JMU-Wearable-Computing/haptic-glove/Images/Tutorial Photos/PlatformIO Setup/bus_io_library.png

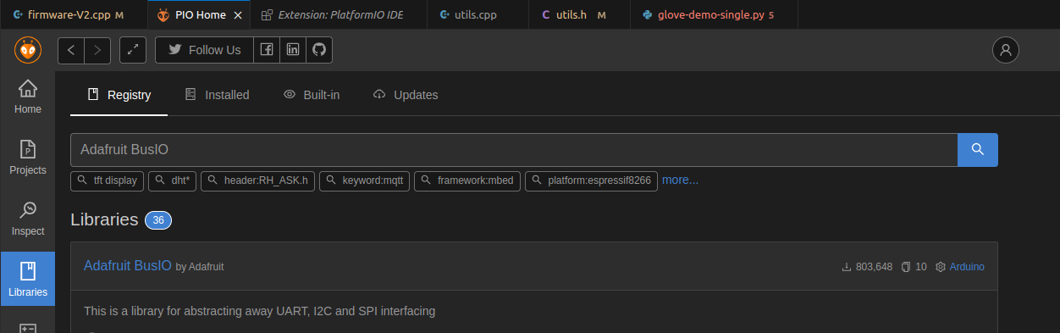
Images/Tutorial Photos/PlatformIO Setup/bus_io_library.png
