JMU-Wearable-Computing/haptic-glove/Images/Tutorial Photos/PlatformIO Setup/file_structure.png

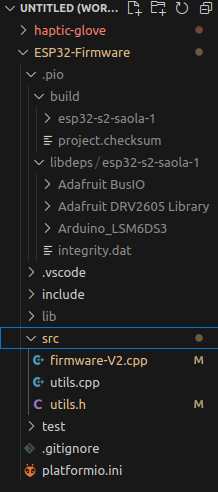
Images/Tutorial Photos/PlatformIO Setup/file_structure.png
