JMU-Wearable-Computing/haptic-glove/Images/Tutorial Photos/PlatformIO Setup/open_serial.png

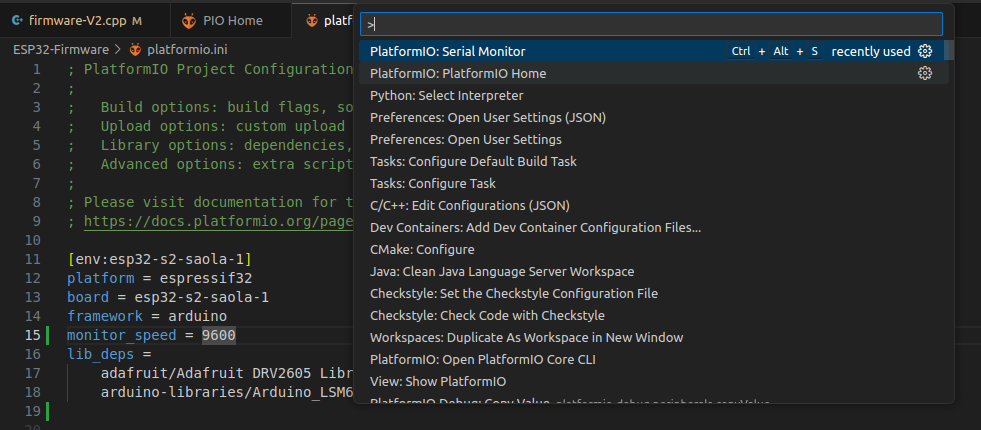
Images/Tutorial Photos/PlatformIO Setup/open_serial.png
