JMU-Wearable-Computing/haptic-glove/Images/Tutorial Photos/PlatformIO Setup/serial_output.png

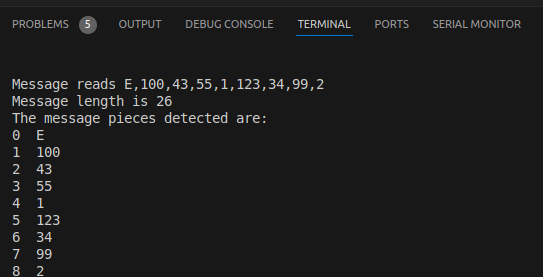
Images/Tutorial Photos/PlatformIO Setup/serial_output.png
