JMU-Wearable-Computing/haptic-glove/Images/Tutorial Photos/PlatformIO Setup/set_baud_rate.png

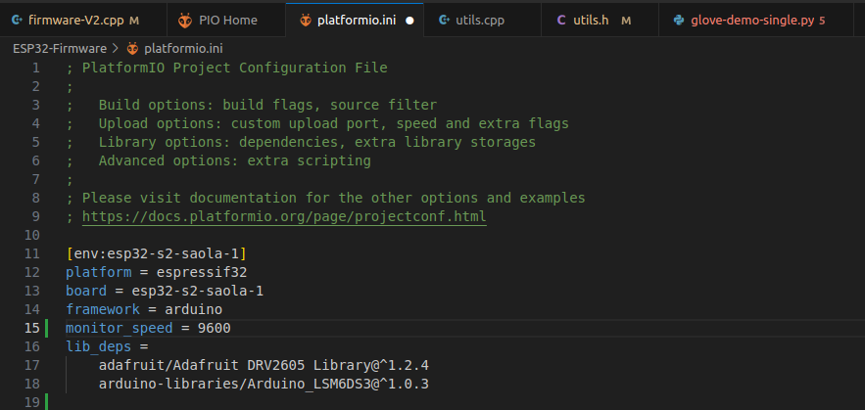
Images/Tutorial Photos/PlatformIO Setup/set_baud_rate.png
