JMU-Wearable-Computing/haptic-glove/Python/joint_angle_test_data_002.csv

Format Version | 1.23 | Take Name | joint_angle_test_data_002 | Take Notes |  | Capture Frame Rate | 120.000000 | Export Frame Rate | 120.000000 | Capture Start Time | 2024-09-20 12.51.27.389 PM | Capture Start Frame | 91932359 | Total Frames in Take | 2987 | Total Exported Frames | 2987 | Rotation Type | Quaternion | Length Units | Millimeters | Coordinate Space | Local
 | Type | Marker | Marker | Marker | Marker | Marker | Marker | Marker | Marker | Marker
 | Name | Elbow | Elbow | Elbow | Hand | Hand | Hand | Shoulder | Shoulder | Shoulder
 | ID | 27E4CEA3EA24707811EF | 27E4CEA3EA24707811EF | 27E4CEA3EA24707811EF | 2808CEA3EA24707811EF | 2808CEA3EA24707811EF | 2808CEA3EA24707811EF | 2805CEA3EA24707811EF | 2805CEA3EA24707811EF | 2805CEA3EA24707811EF
 |  | Position | Position | Position | Position | Position | Position | Position | Position | Position
Frame | Time (Seconds) | X | Y | Z | X | Y | Z | X | Y | Z
0 | 0.000000 | -106.629082 | 28.969299 | 745.029114 | 394.950256 | 6.998325 | 980.493958 | 123.977539 | 14.865740 | 248.449341
1 | 0.008000 | -106.635483 | 28.973684 | 745.034973 | 394.960968 | 6.996509 | 980.489136 | 123.973701 | 14.865225 | 248.452805
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
