JMU-Wearable-Computing/haptic-glove/Python/joint_angle_test_data_005.csv

Format Version | 1.23 | Take Name | joint_angle_test_data_005 | Take Notes |  | Capture Frame Rate | 120.000000 | Export Frame Rate | 120.000000 | Capture Start Time | 2024-09-20 01.28.16.486 PM | Capture Start Frame | 92197447 | Total Frames in Take | 1209 | Total Exported Frames | 1209 | Rotation Type | Quaternion | Length Units | Millimeters | Coordinate Space | Local
 | Type | Marker | Marker | Marker | Marker | Marker | Marker | Marker | Marker | Marker
 | Name | Elbow | Elbow | Elbow | Hand | Hand | Hand | Shoulder | Shoulder | Shoulder
 | ID | 289DCEA3EA24707811EF | 289DCEA3EA24707811EF | 289DCEA3EA24707811EF | 289CCEA3EA24707811EF | 289CCEA3EA24707811EF | 289CCEA3EA24707811EF | 289ACEA3EA24707811EF | 289ACEA3EA24707811EF | 289ACEA3EA24707811EF
 |  | Position | Position | Position | Position | Position | Position | Position | Position | Position
Frame | Time (Seconds) | X | Y | Z | X | Y | Z | X | Y | Z
0 | 0.000000 | -500.934601 | 1016.669861 | 1447.266968 | -338.306641 | 849.596924 | 1579.394409 | -453.653961 | 1358.664795 | 1405.358643
1 | 0.008000 | -499.620697 | 1016.606445 | 1447.831787 | -332.645905 | 852.768494 | 1579.212402 | -453.719696 | 1358.724243 | 1405.263306
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
