JMU-Wearable-Computing/haptic-glove/Python/joint_angle_test_data_006.csv

Format Version | 1.23 | Take Name | joint_angle_test_data_006 | Take Notes |  | Capture Frame Rate | 120.000000 | Export Frame Rate | 120.000000 | Capture Start Time | 2024-09-25 02.39.40.245 PM | Capture Start Frame | 144550676 | Total Frames in Take | 3130 | Total Exported Frames | 3130 | Rotation Type | Quaternion | Length Units | Millimeters | Coordinate Space | Local
 | Type | Marker | Marker | Marker | Marker | Marker | Marker | Marker | Marker | Marker
 | Name | Elbow | Elbow | Elbow | Hand | Hand | Hand | Shoulder | Shoulder | Shoulder
 | ID | 295BCEA3EA24707811EF | 295BCEA3EA24707811EF | 295BCEA3EA24707811EF | 2959CEA3EA24707811EF | 2959CEA3EA24707811EF | 2959CEA3EA24707811EF | 2953CEA3EA24707811EF | 2953CEA3EA24707811EF | 2953CEA3EA24707811EF
 |  | Position | Position | Position | Position | Position | Position | Position | Position | Position
Frame | Time (Seconds) | X | Y | Z | X | Y | Z | X | Y | Z
0 | 0.000000 | -357.986481 | 23.156046 | 519.461670 | 173.546631 | 30.231720 | 318.815765 | 195.666138 | 14.611786 | 385.810516
1 | 0.008000 | -357.984253 | 23.146061 | 519.462341 | 173.605820 | 30.106300 | 318.782104 | 195.663895 | 14.608956 | 385.808167
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
