JMU-Wearable-Computing/haptic-glove/Python/joint_angle_test_data_1_001.csv

1.23 | Capture Frame Rate | 120 | Export Frame Rate
Type | Rigid Body | Rigid Body | Rigid Body | Rigid Body | Rigid Body | Rigid Body | Rigid Body | Rigid Body | Rigid Body
Name | Shoulder_Suit | Shoulder_Suit | Shoulder_Suit | Elbow_Suit | Elbow_Suit | Elbow_Suit | Hand_Suit | Hand_Suit | Hand_Suit
ID | 5F10C191754A11EF7E5C15E596CCCB90 | 5F10C191754A11EF7E5C15E596CCCB90 | 5F10C191754A11EF7E5C15E596CCCB90 | 66B905C7754A11EF7E5C15E596CCCB90 | 66B905C7754A11EF7E5C15E596CCCB90 | 66B905C7754A11EF7E5C15E596CCCB90 | 70C6742A754A11EF7E5C15E596CCCB90 | 70C6742A754A11EF7E5C15E596CCCB90 | 70C6742A754A11EF7E5C15E596CCCB90
 | Position | Position | Position | Position | Position | Position | Position | Position | Position
Time (Seconds) | X | Y | Z | X | Y | Z | X | Y | Z
0 | -184.000488 | 1430.728027 | 28.554445 | -229.980042 | 1120.384644 | -6.191123 | -218.839157 | 900.816956 | 105.278915
0.008 | -184.019669 | 1430.710693 | 28.531429 | -230.00647 | 1120.368164 | -6.17447 | -218.86055 | 900.810669 | 105.257973
0.017 | -184.02475 | 1430.683472 | 28.518126 | -230.017319 | 1120.360596 | -6.173347 | -218.916107 | 900.781982 | 105.265892
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
