JMU-Wearable-Computing/haptic-glove/Arduino/Feedback-Pattern-Demos/DRV-demo-basic/DRV-demo-basic.ino

#include <Wire.h>
#include "Adafruit_DRV2605.h"

Adafruit_DRV2605 drv1;
Adafruit_DRV2605 drv2;
#define TCAADDR 0x70

// Select which driver to talk to
void tcaselect(uint8_t i) {
  if (i > 7) return;
 
  Wire.beginTransmission(TCAADDR);
  Wire.write(1 << i);
  Wire.endTransmission();  
}

void setup() {
  Serial.begin(9600);
  Wire.begin();
  Serial.println("Adafruit DRV2605 Basic test");

  // Set up first driver
  tcaselect(0);
  if (! drv1.begin()) {
    Serial.println("Could not find DRV2605");
    while (1) delay(10);
  }
 
  drv1.selectLibrary(1);
  
  // I2C trigger by sending 'go' command 
  // default, internal trigger when sending GO command
  drv1.setMode(DRV2605_MODE_INTTRIG);

  // Set up second driver
  tcaselect(1);
  if (! drv2.begin()) {
    Serial.println("Could not find second DRV2605");
    while (1) delay(10);
  }
 
  drv2.selectLibrary(1);
  
  // I2C trigger by sending 'go' command 
  // default, internal trigger when sending GO command
  drv2.setMode(DRV2605_MODE_INTTRIG);
}

uint8_t effect = 1;

void loop() {
//  Serial.print("Effect #"); Serial.println(effect);

   if (effect == 1) {
    Serial.println("11.2 Waveform Library Effects List");
  }

  if (effect == 1) {
    Serial.println(F("1 − Strong Click - 100%"));
  }
  if (effect == 2) {
    Serial.println(F("2 − Strong Click - 60%"));
  }
  if (effect == 3) {
    Serial.println(F("3 − Strong Click - 30%"));
  }
  if (effect == 4) {
    Serial.println(F("4 − Sharp Click - 100%"));
  }
  if (effect == 5) {
    Serial.println(F("5 − Sharp Click - 60%"));
  }
  if (effect == 6) {
    Serial.println(F("6 − Sharp Click - 30%"));
  }
  if (effect == 7) {
    Serial.println(F("7 − Soft Bump - 100%"));
  }
  if (effect == 8) {
    Serial.println(F("8 − Soft Bump - 60%"));
  }
  if (effect == 9) {
    Serial.println(F("9 − Soft Bump - 30%"));
  }
  if (effect == 10) {
    Serial.println(F("10 − Double Click - 100%"));
  }
  if (effect == 11) {
    Serial.println(F("11 − Double Click - 60%"));
  }
  if (effect == 12) {
    Serial.println(F("12 − Triple Click - 100%"));
  }
  if (effect == 13) {
    Serial.println(F("13 − Soft Fuzz - 60%"));
  }
  if (effect == 14) {
    Serial.println(F("14 − Strong Buzz - 100%"));
  }
  if (effect == 15) {
    Serial.println(F("15 − 750 ms Alert 100%"));
  }
  if (effect == 16) {
    Serial.println(F("16 − 1000 ms Alert 100%"));
  }
  if (effect == 17) {
    Serial.println(F("17 − Strong Click 1 - 100%"));
  }
  if (effect == 18) {
    Serial.println(F("18 − Strong Click 2 - 80%"));
  }
  if (effect == 19) {
    Serial.println(F("19 − Strong Click 3 - 60%"));
  }
  if (effect == 20) {
    Serial.println(F("20 − Strong Click 4 - 30%"));
  }
  if (effect == 21) {
    Serial.println(F("21 − Medium Click 1 - 100%"));
  }
  if (effect == 22) {
    Serial.println(F("22 − Medium Click 2 - 80%"));
  }
  if (effect == 23) {
    Serial.println(F("23 − Medium Click 3 - 60%"));
  }
  if (effect == 24) {
    Serial.println(F("24 − Sharp Tick 1 - 100%"));
  }
  if (effect == 25) {
    Serial.println(F("25 − Sharp Tick 2 - 80%"));
  }
  if (effect == 26) {
    Serial.println(F("26 − Sharp Tick 3 – 60%"));
  }
  if (effect == 27) {
    Serial.println(F("27 − Short Double Click Strong 1 – 100%"));
  }
  if (effect == 28) {
    Serial.println(F("28 − Short Double Click Strong 2 – 80%"));
  }
  if (effect == 29) {
    Serial.println(F("29 − Short Double Click Strong 3 – 60%"));
  }
  if (effect == 30) {
    Serial.println(F("30 − Short Double Click Strong 4 – 30%"));
  }
  if (effect == 31) {
    Serial.println(F("31 − Short Double Click Medium 1 – 100%"));
  }
  if (effect == 32) {
    Serial.println(F("32 − Short Double Click Medium 2 – 80%"));
  }
  if (effect == 33) {
    Serial.println(F("33 − Short Double Click Medium 3 – 60%"));
  }
  if (effect == 34) {
    Serial.println(F("34 − Short Double Sharp Tick 1 – 100%"));
  }
  if (effect == 35) {
    Serial.println(F("35 − Short Double Sharp Tick 2 – 80%"));
  }
  if (effect == 36) {
    Serial.println(F("36 − Short Double Sharp Tick 3 – 60%"));
  }
  if (effect == 37) {
    Serial.println(F("37 − Long Double Sharp Click Strong 1 – 100%"));
  }
  if (effect == 38) {
    Serial.println(F("38 − Long Double Sharp Click Strong 2 – 80%"));
  }
  if (effect == 39) {
    Serial.println(F("39 − Long Double Sharp Click Strong 3 – 60%"));
  }
  if (effect == 40) {
    Serial.println(F("40 − Long Double Sharp Click Strong 4 – 30%"));
  }
  if (effect == 41) {
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
  }
  if (effect == 117) {
    Serial.println(F("117 − Transition Ramp Up Short Sharp 2 – 0 to 50%"));
  }
  if (effect == 118) {
    Serial.println(F("118 − Long buzz for programmatic stopping – 100%"));
  }
  if (effect == 119) {
    Serial.println(F("119 − Smooth Hum 1 (No kick or brake pulse) – 50%"));
  }
  if (effect == 120) {
    Serial.println(F("120 − Smooth Hum 2 (No kick or brake pulse) – 40%"));
  }
  if (effect == 121) {
    Serial.println(F("121 − Smooth Hum 3 (No kick or brake pulse) – 30%"));
  }
  if (effect == 122) {
    Serial.println(F("122 − Smooth Hum 4 (No kick or brake pulse) – 20%"));
  }
  if (effect == 123) {
    Serial.println(F("123 − Smooth Hum 5 (No kick or brake pulse) – 10%"));
  }

  // set the effect to play for driver 1
  tcaselect(0);
  drv1.setWaveform(0, effect);  // play effect 
  drv1.setWaveform(1, 0);       // end waveform

  // play the effect!
  drv1.go();

  // wait a bit
  delay(500);

  // set the effect to play for driver 2
  tcaselect(1);
  drv2.setWaveform(0, effect);  // play effect 
  drv2.setWaveform(1, 0);       // end waveform

  // play the effect!
  drv2.go();

  // wait a bit
  delay(500);

  effect++;
  if (effect > 117) effect = 1;
}
